GadgetReboot/Phone_SLIM/sketch/ThisIsARecording1.h

#ifndef ThisIsARecording1_H_
#define ThisIsARecording1_H_
 
#if ARDUINO >= 100
#include "Arduino.h"
#else
#include "WProgram.h"
#endif
#include "mozzi_pgmspace.h"
 
#define ThisIsARecording1_NUM_CELLS 60209
#define ThisIsARecording1_SAMPLERATE 16384
 
CONSTTABLE_STORAGE(int8_t) ThisIsARecording1_DATA [] = {-1, -1, 0, -1, 0, -1,
-1, -1, 0, -1, -1, -1, 0, -1, 0, -1, 0, -1, -1, -1, -1, -1, -1, -1, -1, 0, -1,
-1, -1, -1, -1, -1, -1, 0, -1, 0, -1, 0, -1, -1, -1, -1, -1, -1, -1, -1, 0, -1,
0, -1, -1, 0, -1, 0, -1, 0, -1, 0, -1, -1, -1, 0, -1, -1, 0, -1, -1, -1, 0, -1,
-1, -1, -1, -1, -1, 0, -1, 0, 0, -1, 0, 0, 0, 0, -1, 0, -1, -1, 0, -1, 0, -1, 0,
0, 0, -1, -1, -1, -1, -1, -1, 0, -1, 0, -1, 0, -1, 0, -1, -1, -1, -1, 0, -1, -1,
-1, -1, -1, -1, -1, -1, -1, -1, -1, 0, -1, -1, -1, 0, -1, -1, -1, -1, -1, -1,
-1, -1, -1, -1, -1, -1, -1, -1, 0, -1, -1, 0, -1, -1, -1, -1, -1, 0, -1, -1, -1,
-1, -1, -1, 0, -1, 0, -1, 0, -1, -1, 0, -1, -1, -1, -1, 0, 0, -1, -1, -1, -1,
-1, -1, -1, -1, -1, -1, -1, -1, 0, -1, -1, -1, -1, -1, -1, -1, -1, -1, -1, 0, 0,
0, -1, -1, -1, -1, -1, -1, -1, -1, -1, -1, -1, -1, -1, -1, -1, -1, -1, -1, -1,
-1, -1, -1, -1, -1, -1, -1, -1, -1, -1, -1, -1, -1, -1, 0, -1, -1, -1, -1, -1,
-1, -1, -1, -1, -1, -1, -1, -1, -1, -1, -1, -1, -1, 0, -1, -1, -1, -1, -1, -1,
-1, -1, -1, -1, 0, -1, 0, -1, 0, -1, -1, -1, -1, -1, 0, 0, -1, -1, -1, -1, -1,
-1, 0, -1, -1, -1, -1, -1, 0, -1, -1, -1, -1, -1, -1, -1, -1, -1, -1, -1, -1,
-1, -1, 0, -1, 0, -1, 0, -1, -1, -1, -1, -1, -1, -1, -1, -1, -1, -1, -1, -1, -1,
-1, -1, -1, -1, -1, -1, -1, -1, -1, 0, -1, -1, -1, -1, -1, -1, -1, -1, -1, -1,
-1, -1, -1, -1, -1, -1, -1, -1, -1, -1, -1, -1, -1, -1, 0, -1, 0, -1, -1, -1,
-1, -1, -1, -1, -1, -1, -1, 0, -1, -1, -1, -1, -1, -1, -1, -1, -1, -1, -1, -1,
-1, -1, 0, -1, 0, -1, -1, -1, -1, -1, -1, -1, -1, -1, 0, -1, -1, -1, -1, -1, -1,
-1, -1, -1, -1, -1, -1, -1, -1, 0, -1, -1, -1, -1, -1, -1, -1, -1, -1, -1, -1,
-1, -1, -1, 0, -1, -1, -1, 0, -1, 0, -1, -1, -1, -1, -1, -1, -1, -1, -1, 0, -1,
-1, -1, -1, -1, 0, -1, 0, -1, -1, -1, -1, 0, -1, 0, -1, -1, -1, -1, -1, -1, -1,
-1, -1, -1, 0, -1, -1, -1, -1, -1, -1, -1, 0, -1, -1, -1, -1, -1, -1, 0, -1, -1,
-1, 0, -1, -1, -1, -1, 0, -1, -1, -1, -1, -1, -1, -1, -1, -1, -1, -1, -1, -1,
-1, -1, -1, -1, 0, -1, -1, -1, -1, -1, 0, -1, -1, 0, -1, -1, -1, -1, 0, -1, 0,
-1, 0, -1, -1, -1, -1, -1, -1, -1, -1, -1, -1, -1, -1, -1, -1, -1, -1, -1, -1,
-1, -1, -1, -1, -1, -1, -1, -1, -1, -1, -1, -1, -1, -1, -1, -1, -1, -1, -1, -1,
-1, -1, -1, -1, -1, -1, -1, -1, -1, -1, -1, -1, -1, -1, -1, -1, -1, -1, -1, -1,
-1, 0, -1, 0, -1, 0, -1, -1, -1, -1, -1, -1, -1, -1, -1, -1, -1, -1, -1, -1, -1,
-1, -1, -1, -1, -1, -1, -1, -1, -1, -1, -1, -1, -1, -1, -1, -1, -1, -1, -1, -1,
-1, -1, -1, -1, -1, -1, -1, -1, -1, -1, -1, -1, -1, -1, -1, -1, -1, -1, -1, -1,
-1, -1, -1, -1, -1, -1, -1, -1, -1, 0, -1, 0, -1, 0, -1, 0, -1, 0, -1, 0, -1,
-1, -1, -1, -1, -1, 0, -1, -1, 0, -1, -1, -1, -1, -1, -1, -1, -1, -1, -1, 0, -1,
0, -1, -1, -1, -1, -1, -1, -1, 0, -1, 0, -1, 0, -1, 0, -1, 0, -1, -1, 0, -1, 0,
-1, -1, 0, -1, -1, -1, -1, -1, 0, -1, 0, 0, 0, -1, 0, -1, -1, -1, -1, -1, -1, 0,
-1, -1, -1, 0, 0, 0, -1, 0, -1, 0, -1, -1, -1, -1, 0, -1, 0, -1, -1, 0, -1, -1,
-1, -1, 0, -1, -1, -1, -1, 0, 0, -1, -1, -1, 0, -1, 0, -1, 0, -1, 0, -1, -1, -1,
-1, 0, -1, -1, -1, 0, 0, -1, -1, -1, 0, -1, 0, -1, -1, 0, -1, 0, -1, 0, -1, -1,
-1, -1, -1, 0, -1, -1, -1, -1, -1, -1, 0, -1, 0, -1, 0, 0, -1, 0, -1, 0, -1, 0,
0, 0, -1, -1, -1, -1, -1, -1, 0, -1, 0, -1, 0, 0, -1, 0, -1, -1, -1, -1, -1, -1,
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

#endif /* ThisIsARecording1_H_ */
